uawortu/BREAN/Renders,Images/2.jpg

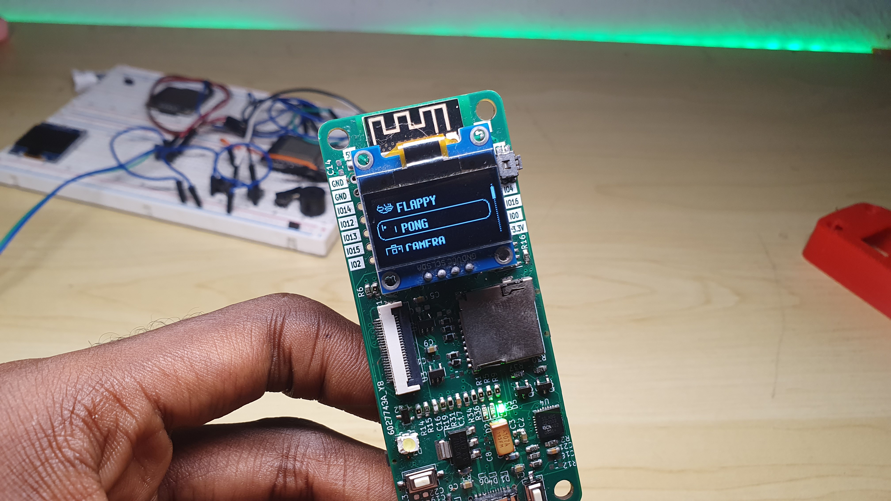
Renders,Images/2.jpg
