uawortu/BREAN/Renders,Images/4.jpg

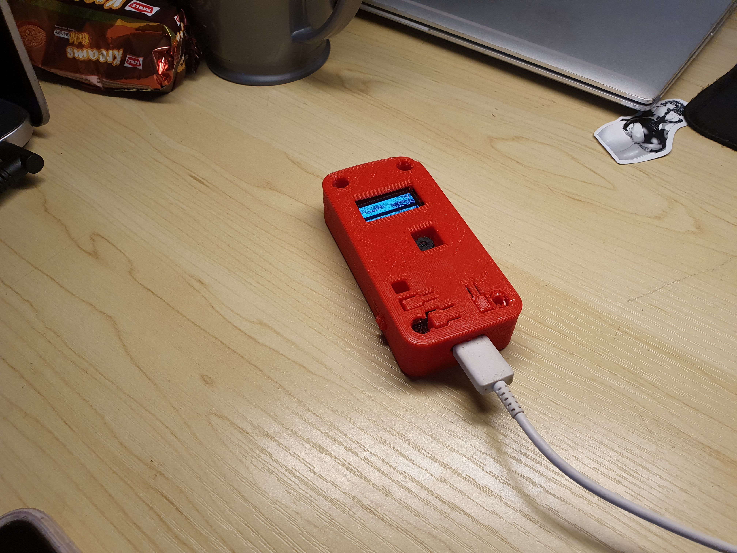
Renders,Images/4.jpg
