uawortu/BREAN/Renders,Images/5.jpg

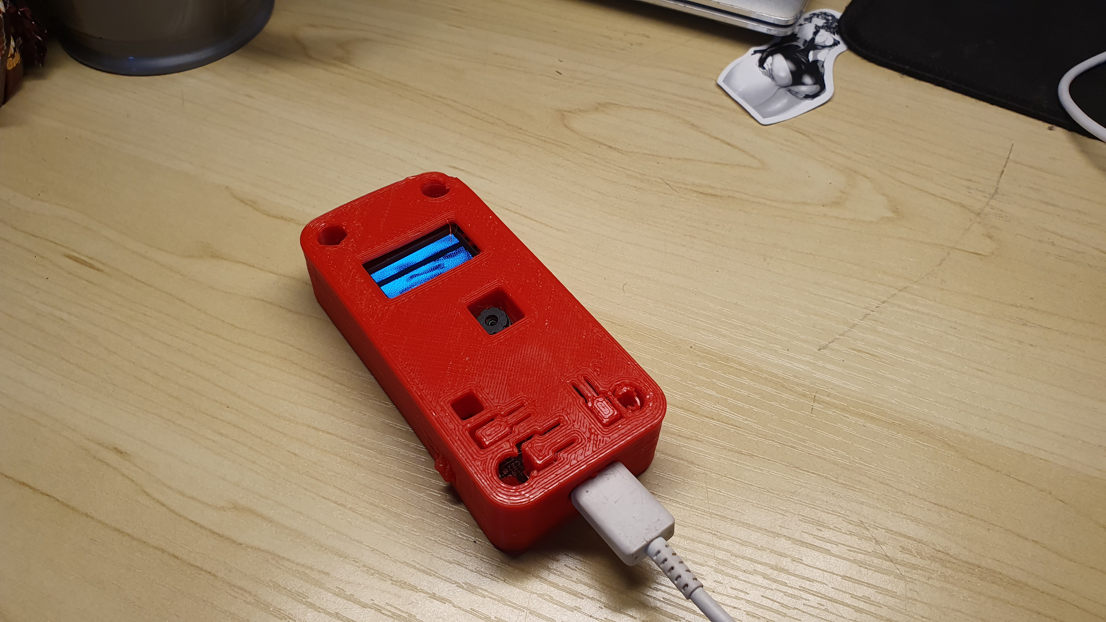
Renders,Images/5.jpg
