uawortu/BREAN/Renders,Images/6.PNG

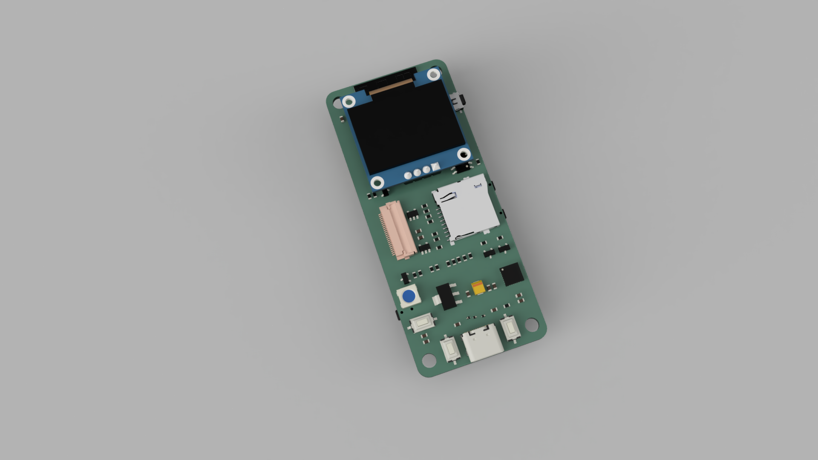
Renders,Images/6.PNG
