uawortu/BREAN/Renders,Images/7.jpg

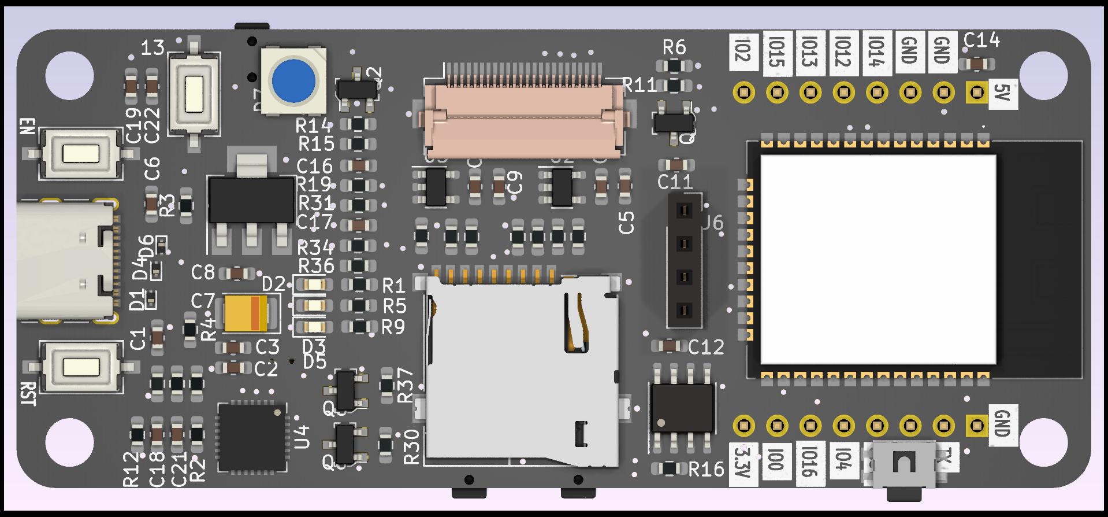
Renders,Images/7.jpg
