uawortu/BREAN/Renders,Images/8.png

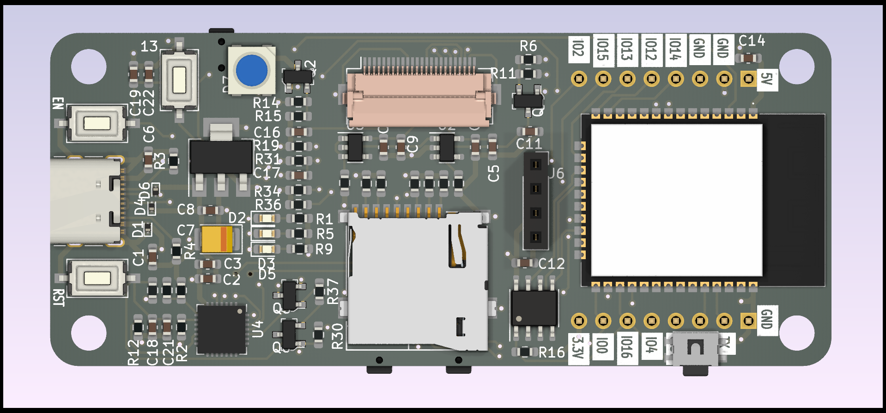
Renders,Images/8.png
