uawortu/BREAN/Renders,Images/9.png

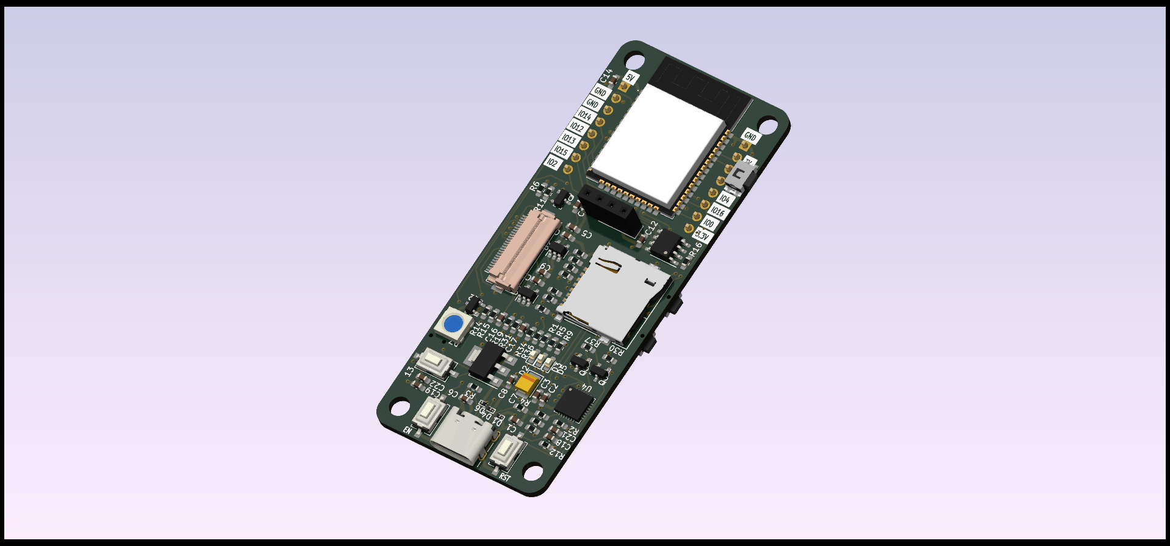
Renders,Images/9.png
