uawortu/BREAN/Renders,Images/10.jpg

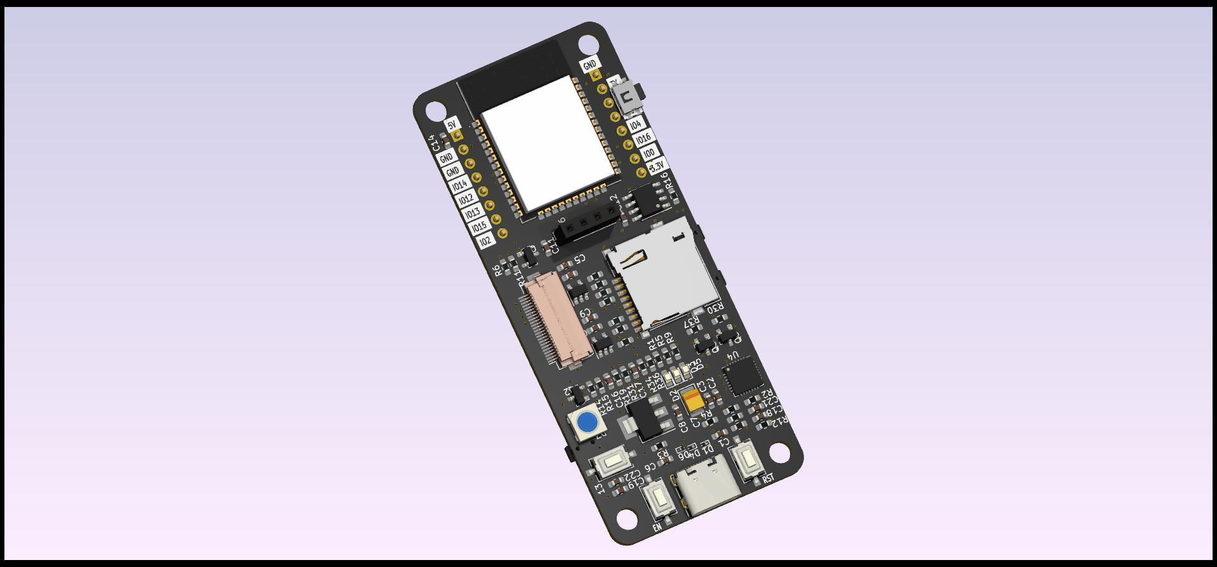
Renders,Images/10.jpg
