uawortu/BREAN/Renders,Images/11.png

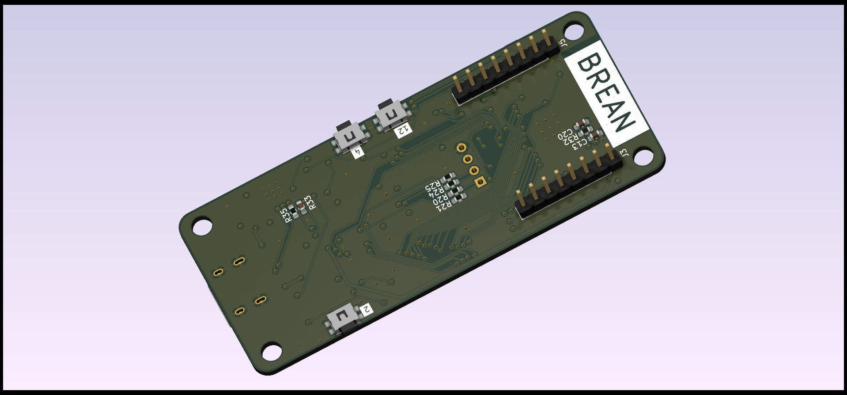
Renders,Images/11.png
