uawortu/BREAN/Renders,Images/12.jpg

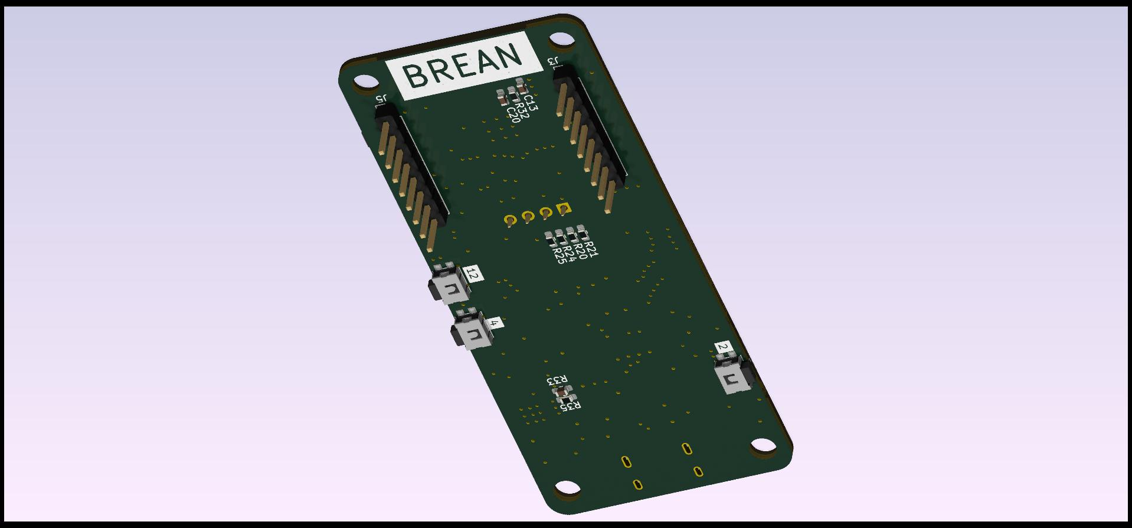
Renders,Images/12.jpg
