uawortu/BREAN/Renders,Images/13.png

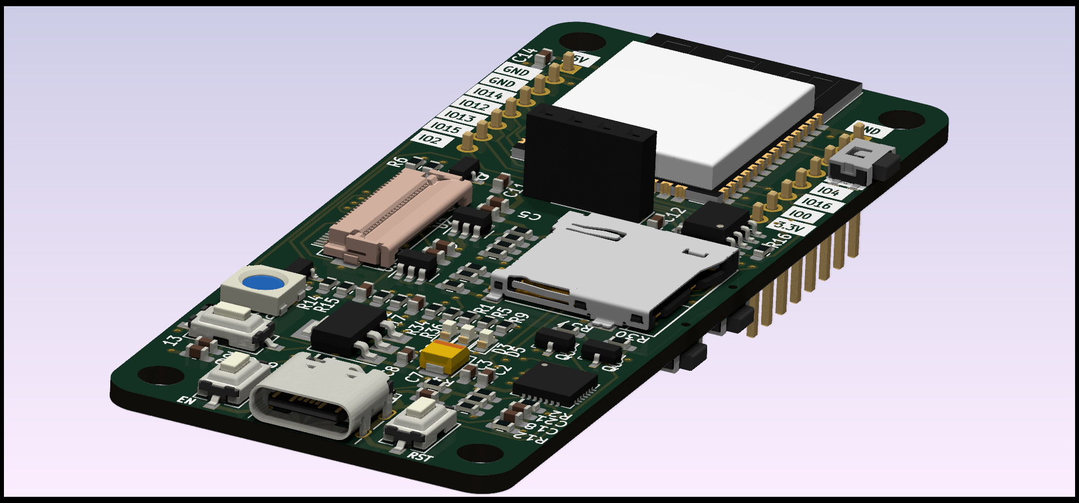
Renders,Images/13.png
