uawortu/BREAN/Renders,Images/14.png

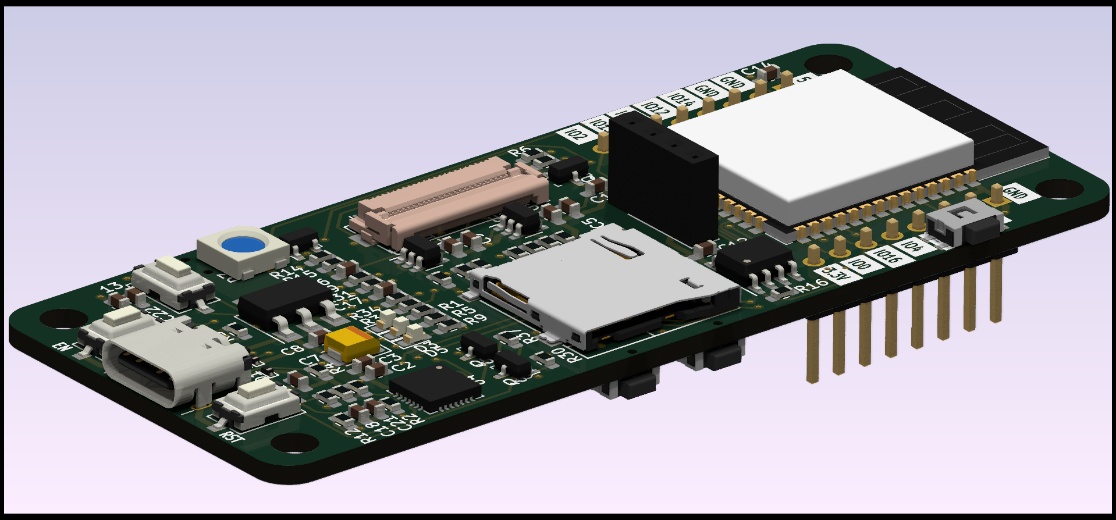
Renders,Images/14.png
