uawortu/BREAN/Renders,Images/15.png

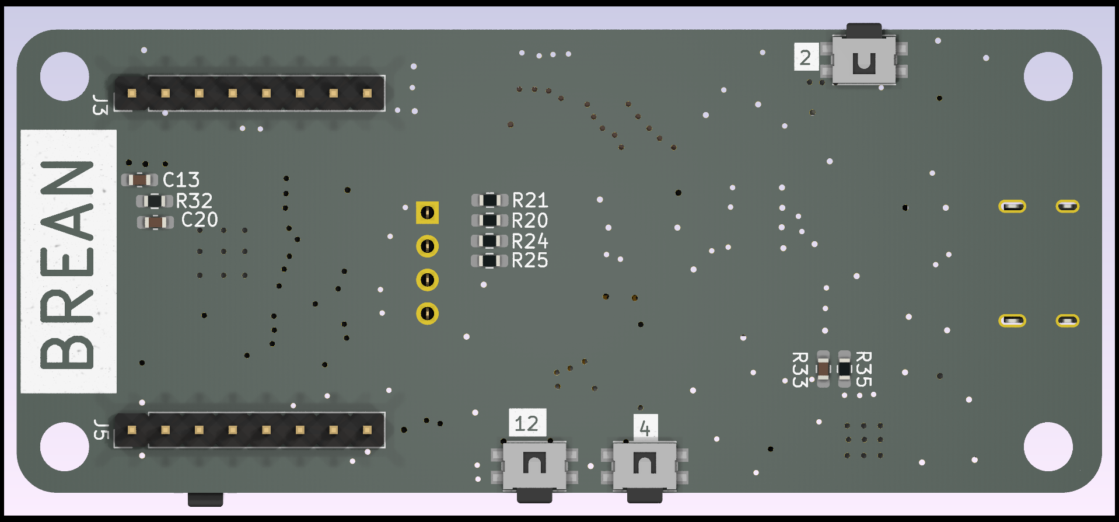
Renders,Images/15.png
