uawortu/BREAN/Renders,Images/16.png

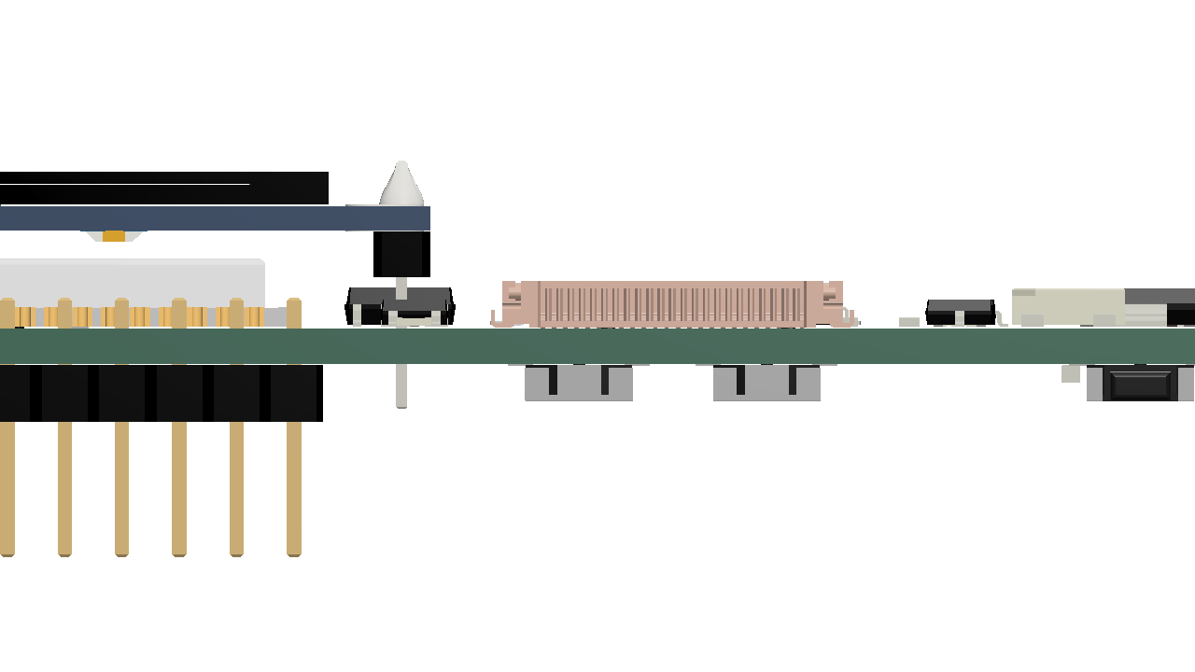
Renders,Images/16.png
