uawortu/BREAN/Renders,Images/18.png

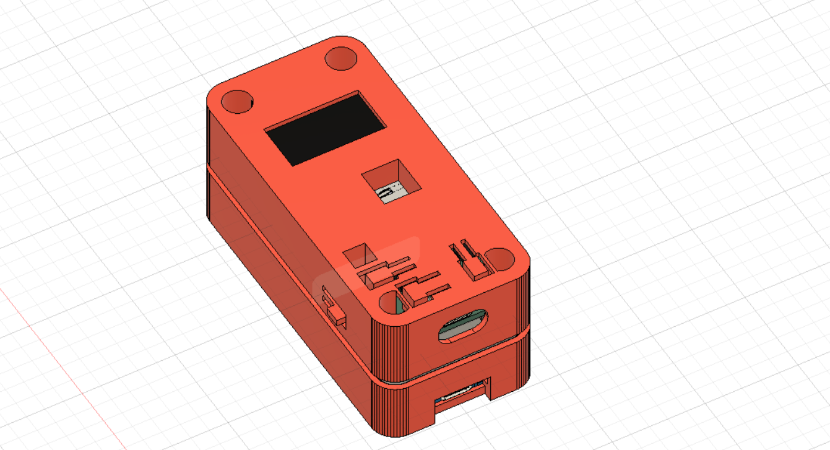
Renders,Images/18.png
