uawortu/BREAN/Renders,Images/19.jpg

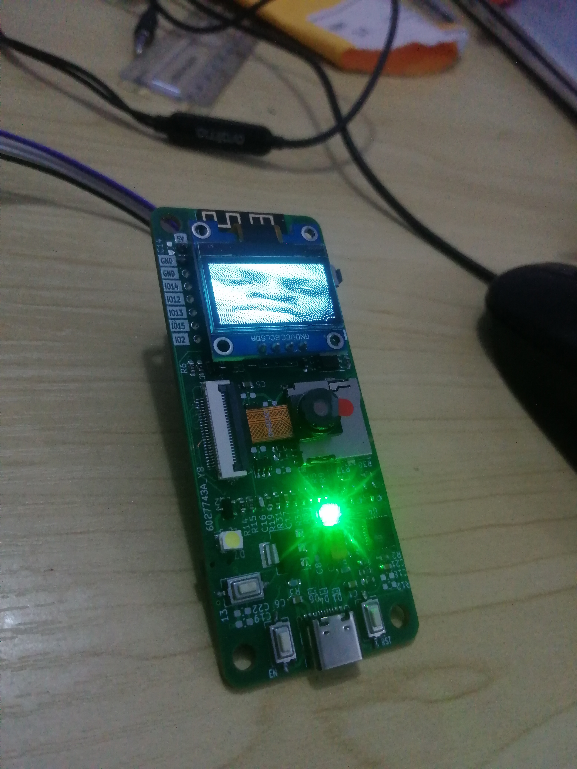
Renders,Images/19.jpg
