uawortu/BREAN/Renders,Images/20.jpg

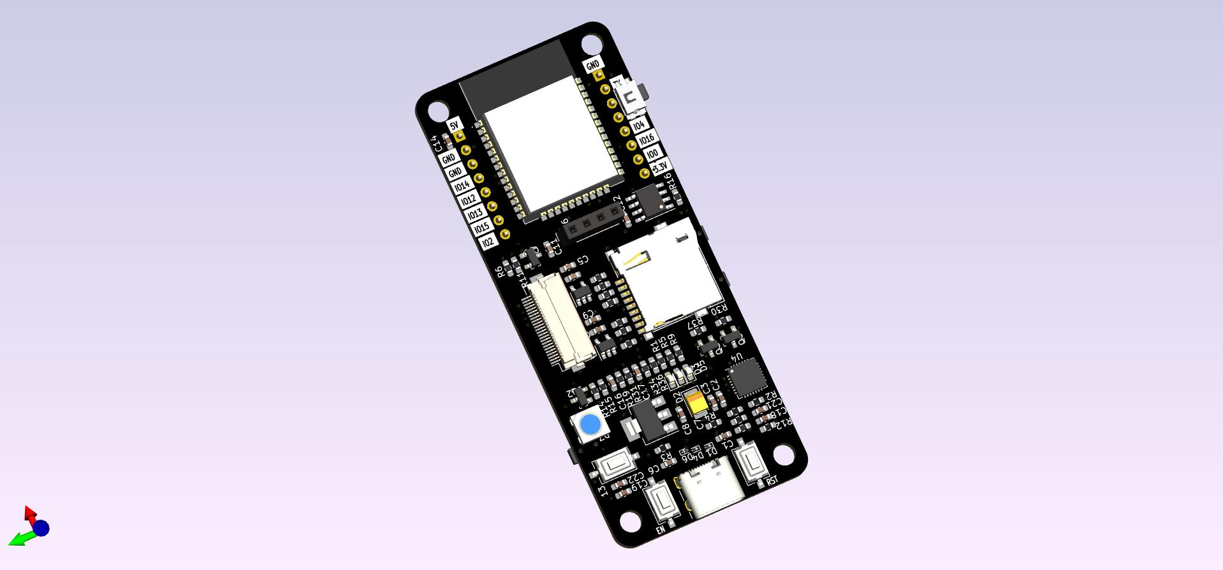
Renders,Images/20.jpg
