uawortu/BREAN/Docs/PCB Layers/ESP32CAM-F_Paste.pdf

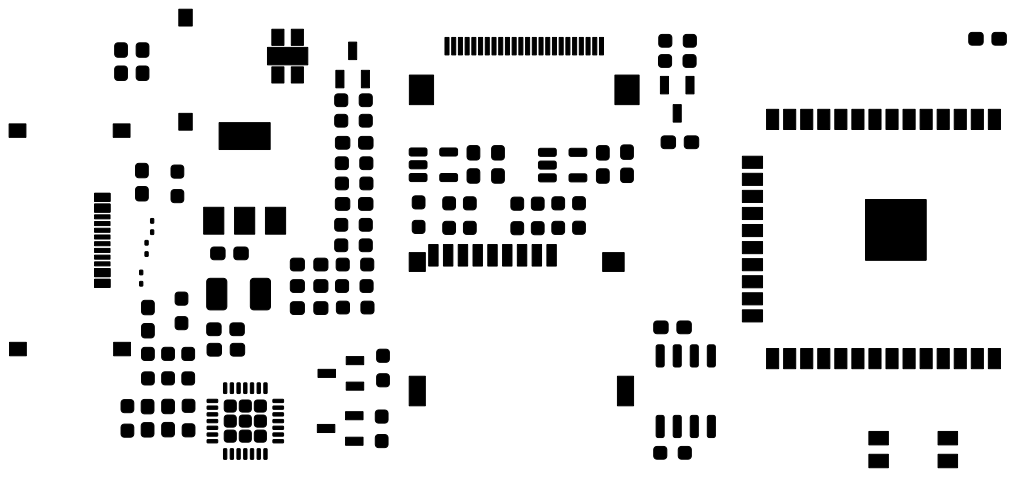
[picture p36: page 1]
