uawortu/BREAN/Docs/PCB Layers/ESP32CAM-F_Silkscreen.pdf

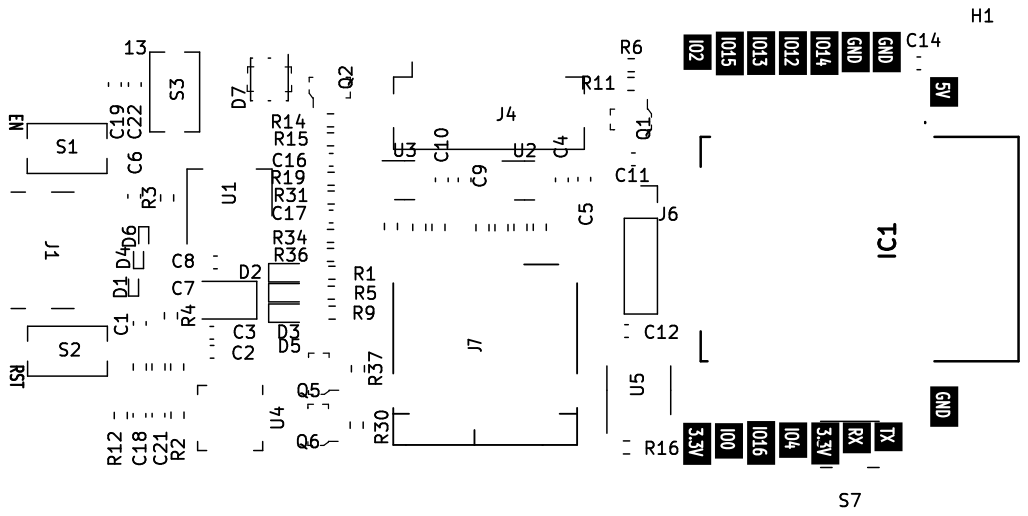
[picture p37: page 1]
