uawortu/BREAN/Docs/PCB Layers/ESP32CAM-GND.pdf

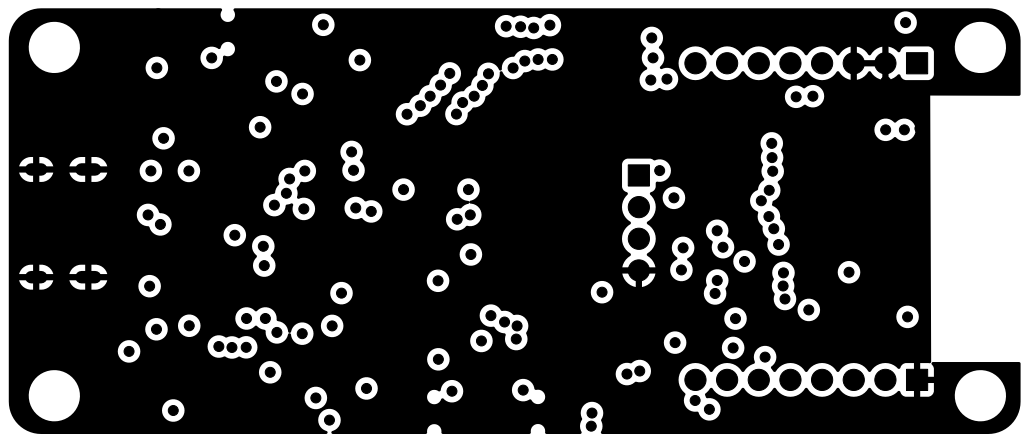
[picture p38: page 1]
